rwb27/Instruments-MechanicalTester/cad/renders/0_main_view.png

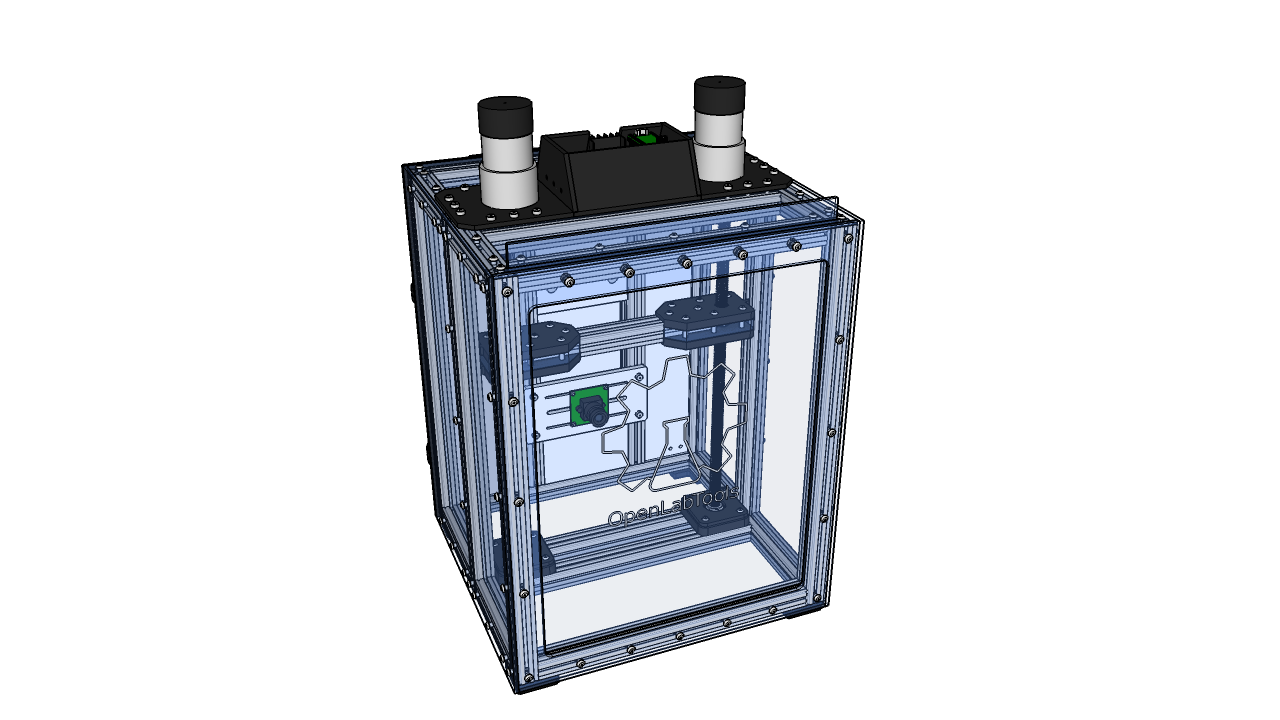
cad/renders/0_main_view.png
