rwb27/Instruments-MechanicalTester/cad/renders/2_top.png

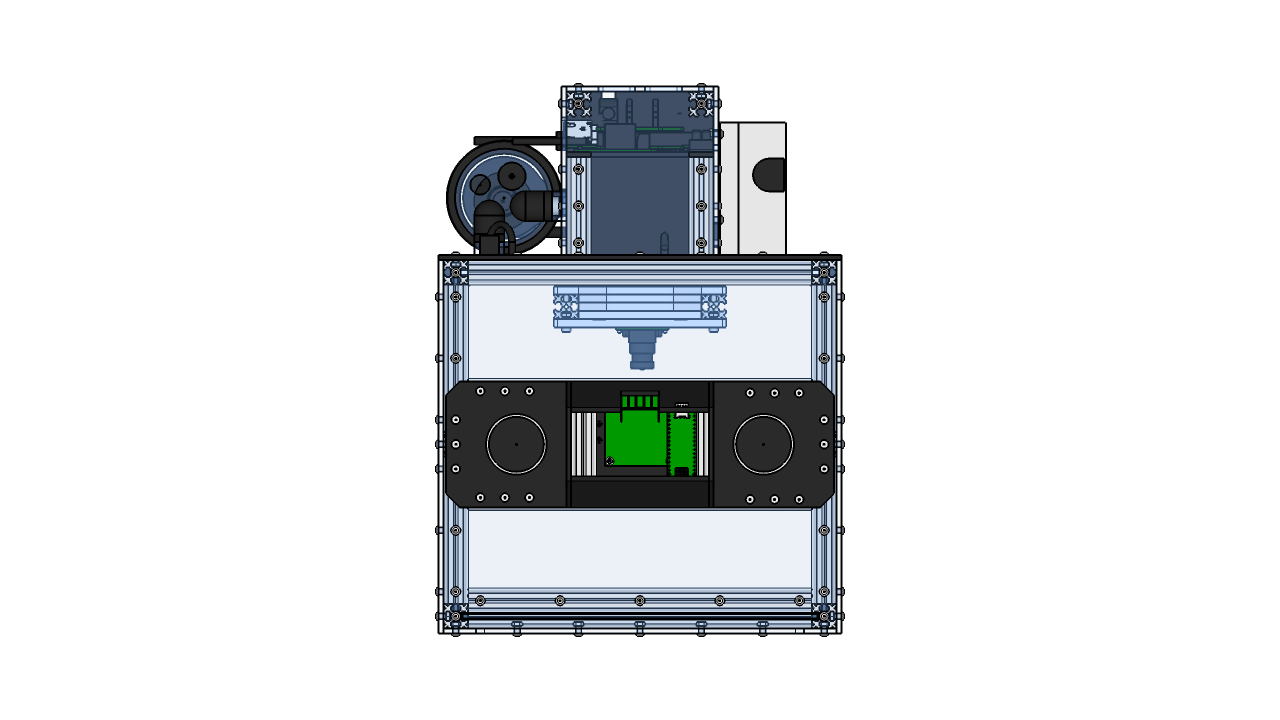
cad/renders/2_top.png
