rwb27/Instruments-MechanicalTester/cad/renders/2_top_small.png

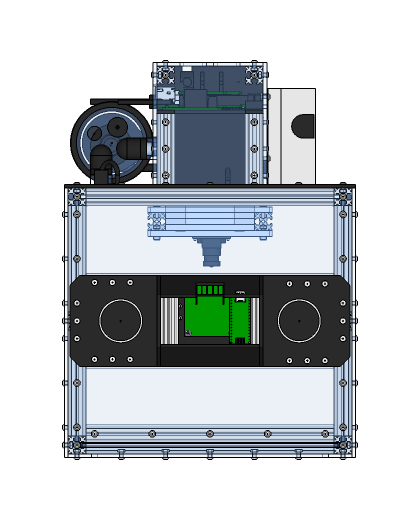
cad/renders/2_top_small.png
