rwb27/Instruments-MechanicalTester/cad/renders/3_front_small.png

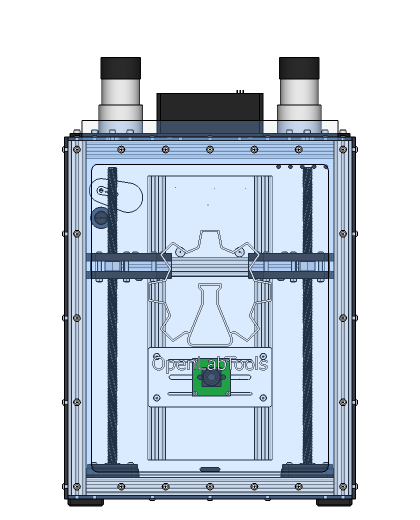
cad/renders/3_front_small.png
