rwb27/Instruments-MechanicalTester/cad/renders/4_right.png

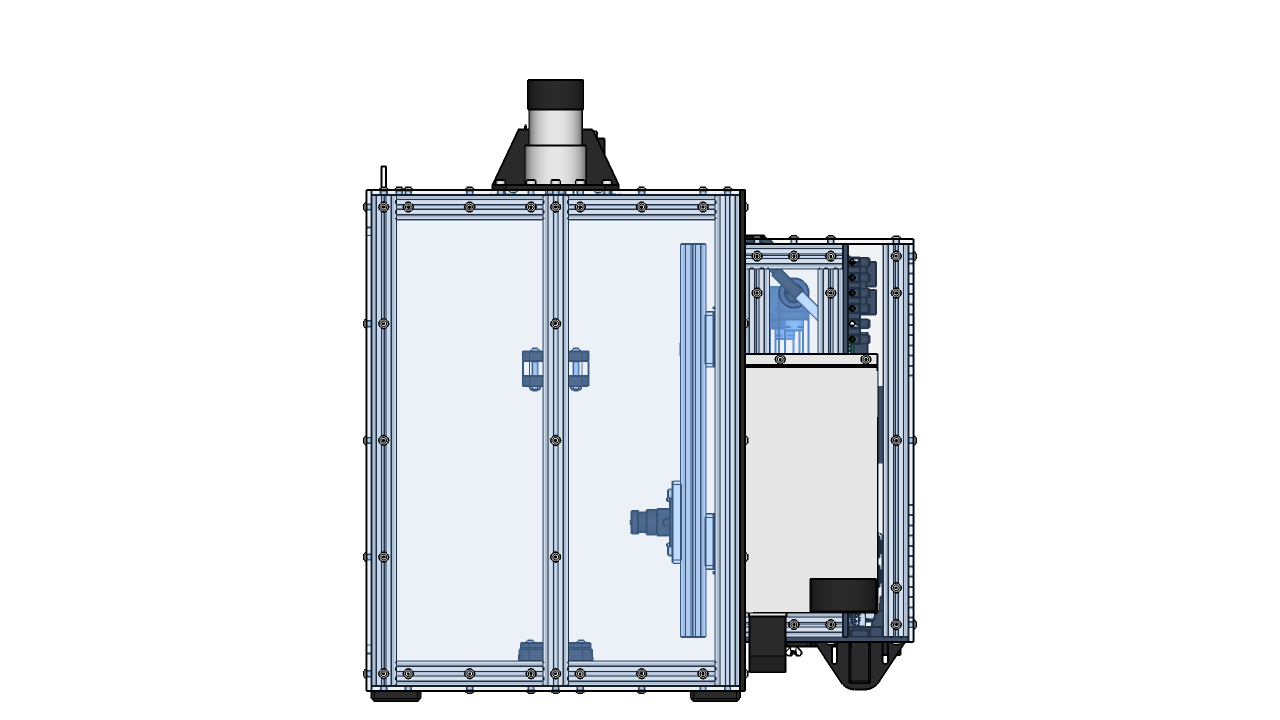
cad/renders/4_right.png
