rwb27/Instruments-MechanicalTester/cad/renders/4_right_small.png

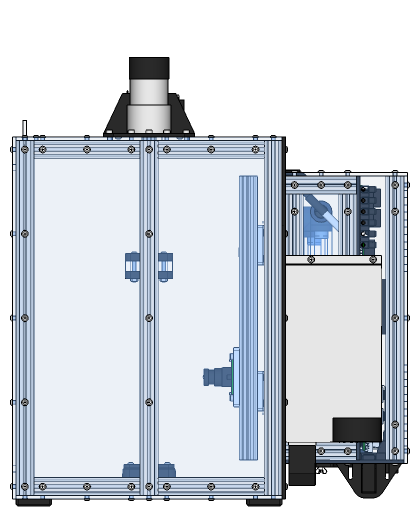
cad/renders/4_right_small.png
