rwb27/Instruments-MechanicalTester/cad/renders/5_back.png

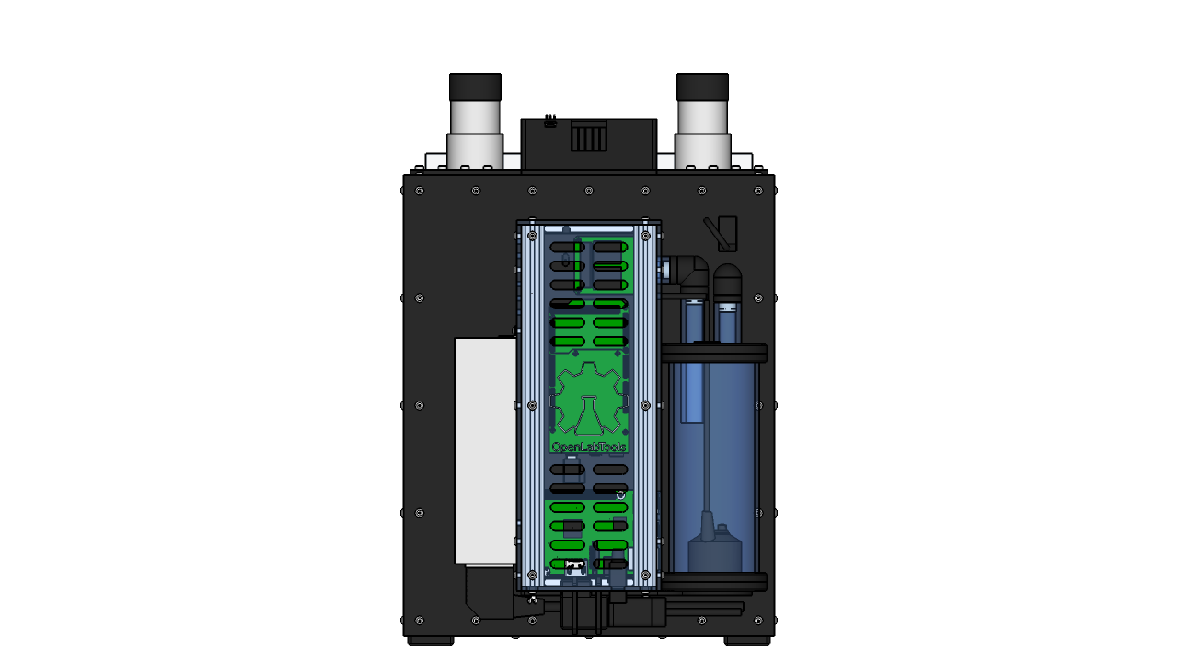
cad/renders/5_back.png
