rwb27/Instruments-MechanicalTester/cad/renders/5_back_small.png

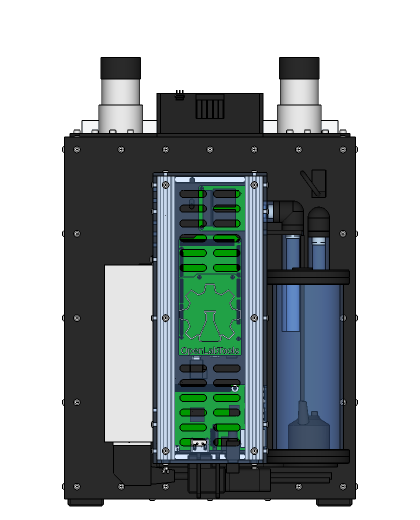
cad/renders/5_back_small.png
