rwb27/Instruments-MechanicalTester/cad/renders/8_cross_section.png

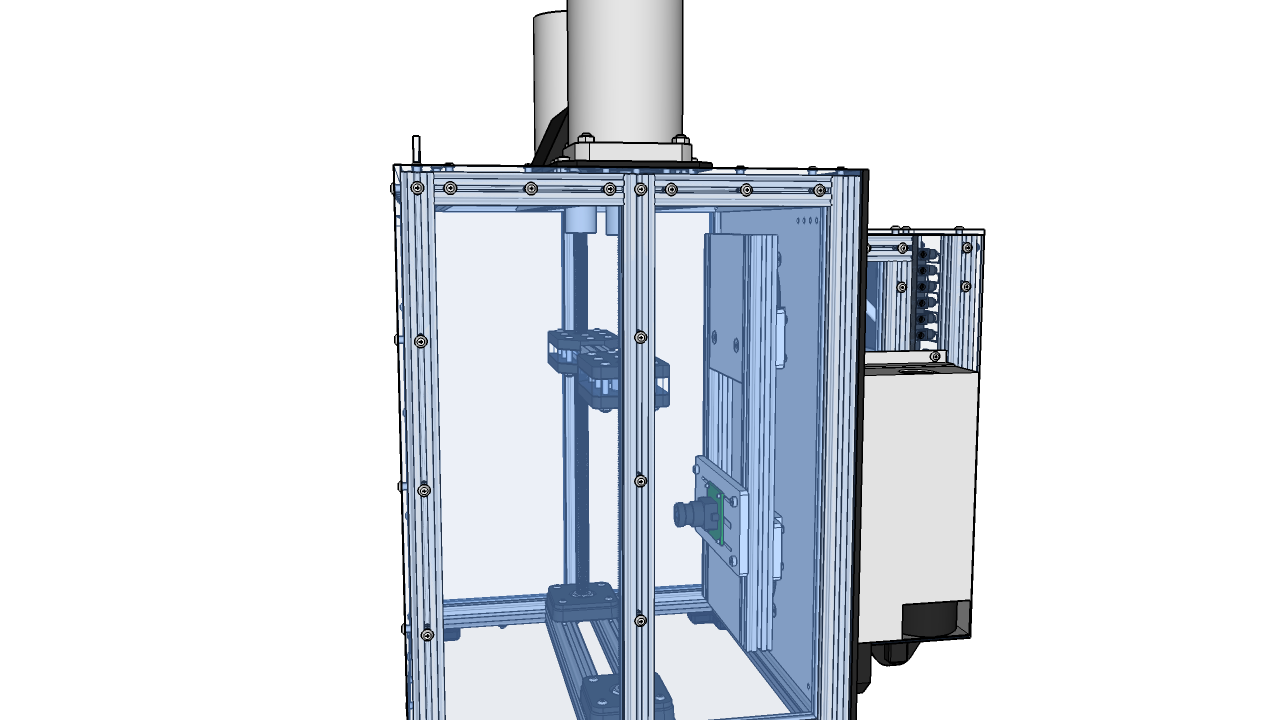
cad/renders/8_cross_section.png
