rwb27/Instruments-MechanicalTester/cad/renders/8_cross_section_small.png

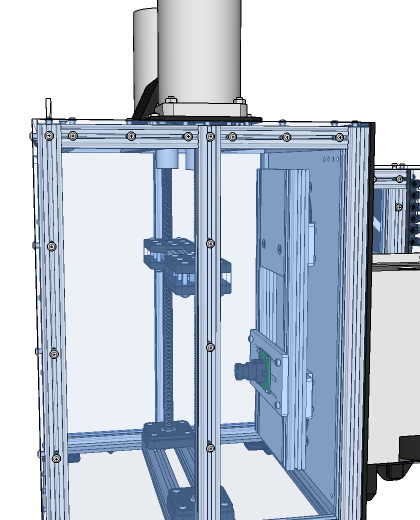
cad/renders/8_cross_section_small.png
