rwb27/Instruments-MechanicalTester/docs/images/instrument_views.jpg

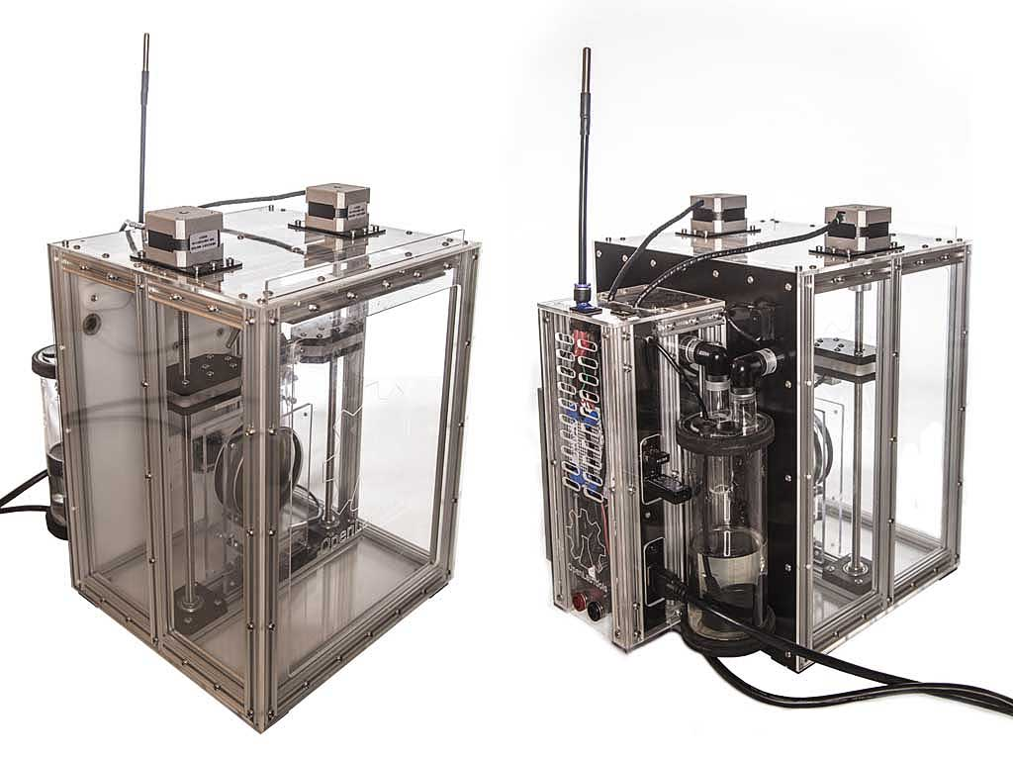
docs/images/instrument_views.jpg
