rwb27/Instruments-MechanicalTester/cad/panels/dxf_files/servo_flap.dxf

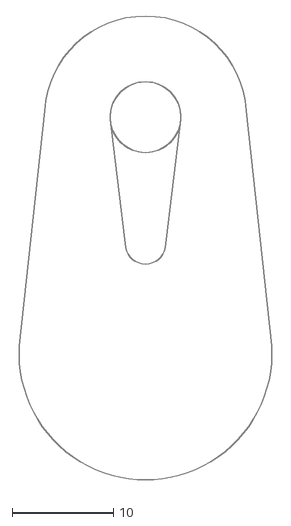
[picture p31: CAD file, 2016-01-02]
cad/panels/dxf_files/servo_flap.dxf
25.5 x 46.5
