rwb27/Instruments-MechanicalTester/cad/panels/dxf_files/humidity_rubber_bumper_bottom.dxf

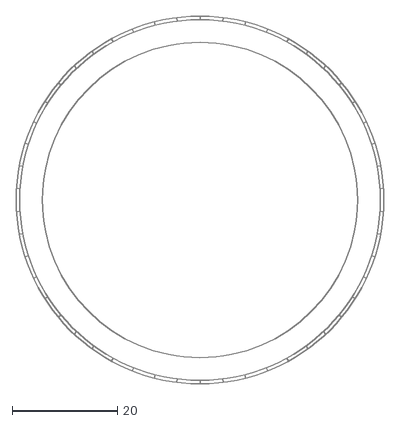
[picture p33: CAD file, 2016-01-02]
cad/panels/dxf_files/humidity_rubber_bumper_bottom.dxf
70.0 x 70.0
