rwb27/Instruments-MechanicalTester/cad/panels/dxf_files/humidity_end_cap.dxf

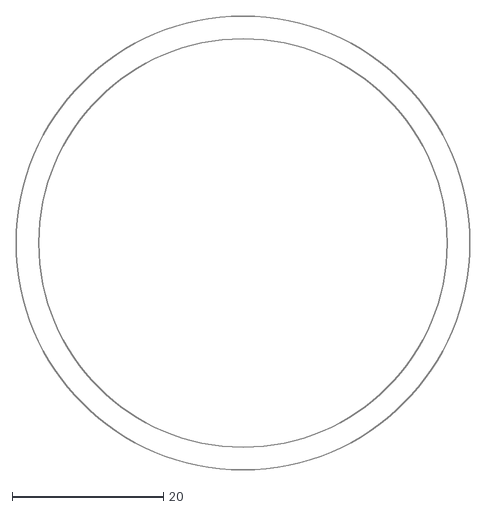
[picture p34: CAD file, 2016-01-02]
cad/panels/dxf_files/humidity_end_cap.dxf
60.0 x 60.0
