rwb27/Instruments-MechanicalTester/cad/panels/dxf_files/fan_mounting.dxf

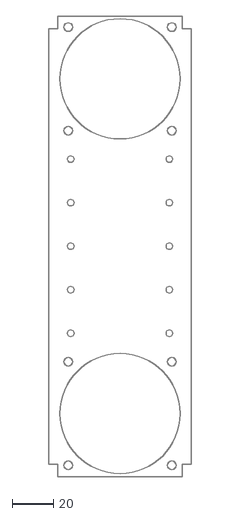
[picture p35: CAD file, 2016-01-02]
cad/panels/dxf_files/fan_mounting.dxf
69.0 x 222.0
