rwb27/Instruments-MechanicalTester/cad/panels/dxf_files/rear_module_back_double_glazing.dxf

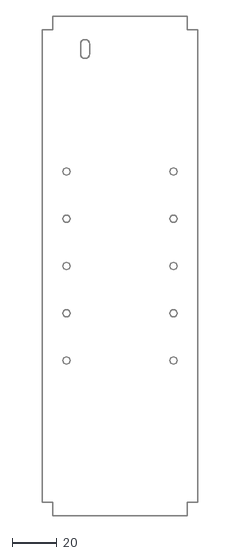
[picture p36: CAD file, 2016-01-02]
cad/panels/dxf_files/rear_module_back_double_glazing.dxf
69.0 x 222.0
