rwb27/Instruments-MechanicalTester/cad/panels/dxf_files/heater_reflector_plate.dxf

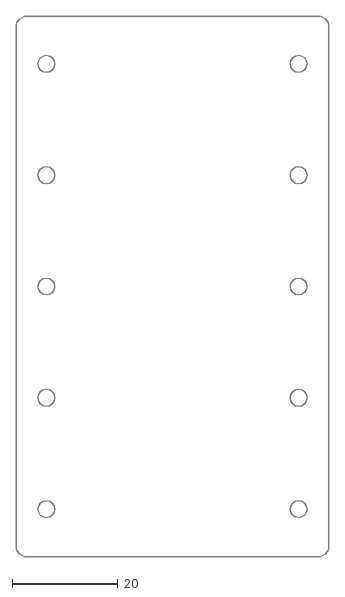
[picture p37: CAD file, 2016-01-02]
cad/panels/dxf_files/heater_reflector_plate.dxf
59.0 x 102.0
