rwb27/Instruments-MechanicalTester/cad/panels/dxf_files/rear_module_humidity_side.dxf

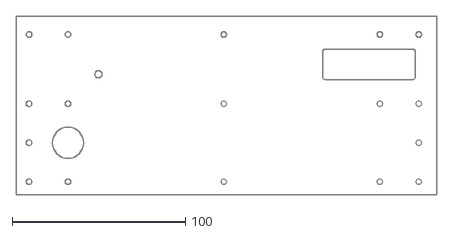
[picture p38: CAD file, 2016-01-01]
cad/panels/dxf_files/rear_module_humidity_side.dxf
243.0 x 103.0
