rwb27/Instruments-MechanicalTester/cad/panels/dxf_files/rear_module_bottom_face.dxf

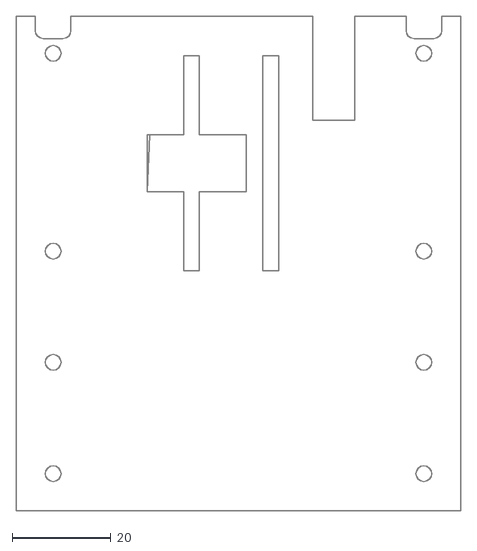
[picture p39: CAD file, 2016-01-01]
cad/panels/dxf_files/rear_module_bottom_face.dxf
90.0 x 100.0
