rwb27/Instruments-MechanicalTester/cad/panels/dxf_files/rear_module_electronics.dxf

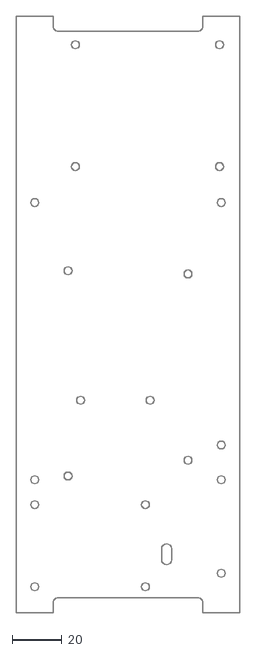
[picture p40: CAD file, 2016-01-01]
cad/panels/dxf_files/rear_module_electronics.dxf
90.0 x 240.0
