rwb27/Instruments-MechanicalTester/cad/panels/dxf_files/hdmi_support_2.dxf

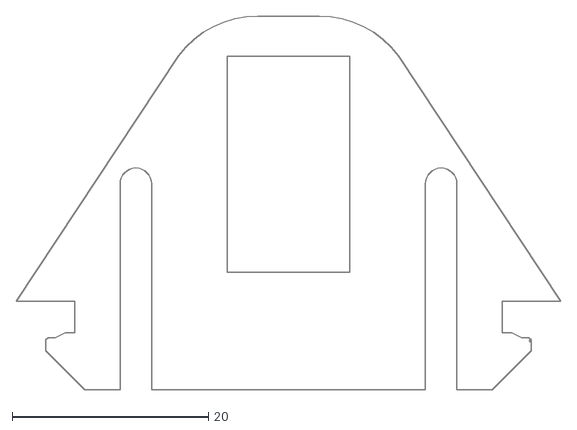
[picture p41: CAD file, 2015-12-31]
cad/panels/dxf_files/hdmi_support_2.dxf
55.5 x 38.1
