rwb27/Instruments-MechanicalTester/cad/panels/dxf_files/rear_module_back_face.dxf

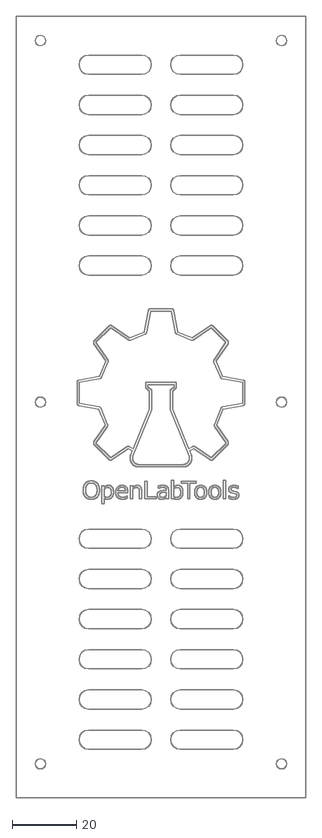
[picture p43: CAD file, 2015-12-28]
cad/panels/dxf_files/rear_module_back_face.dxf
90.0 x 243.0
