rwb27/Instruments-MechanicalTester/cad/panels/dxf_files/nema_17_mount.dxf

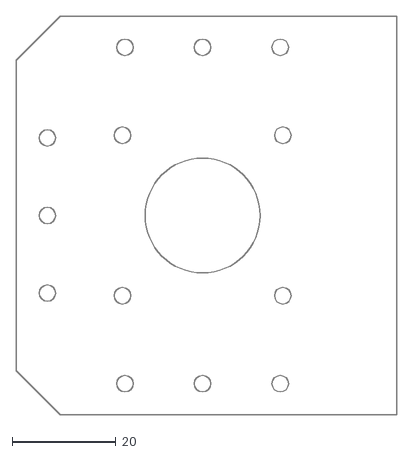
[picture p45: CAD file, 2015-12-27]
cad/panels/dxf_files/nema_17_mount.dxf
73.5 x 77.0
