rwb27/Instruments-MechanicalTester/cad/panels/dxf_files/gantry_spacer.dxf

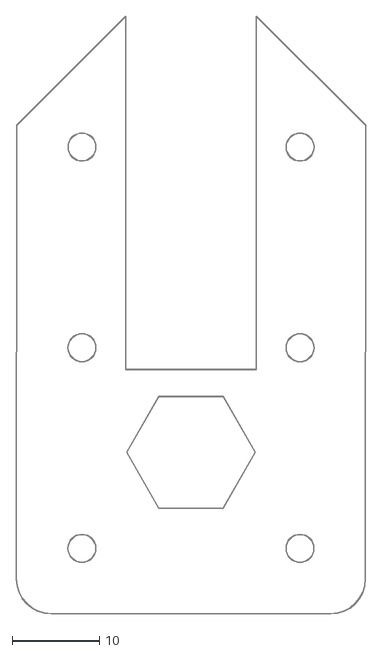
[picture p46: CAD file, 2015-12-23]
cad/panels/dxf_files/gantry_spacer.dxf
40.0 x 68.5
