rwb27/Instruments-MechanicalTester/cad/panels/dxf_files/front_frame.dxf

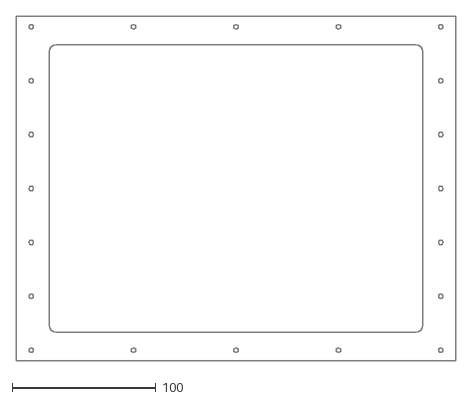
[picture p47: CAD file, 2015-12-23]
cad/panels/dxf_files/front_frame.dxf
306.0 x 240.0
