rwb27/Instruments-MechanicalTester/cad/panels/dxf_files/delrin_plate.dxf

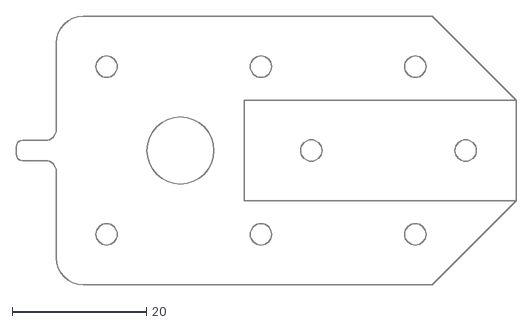
[picture p48: CAD file, 2015-12-23]
cad/panels/dxf_files/delrin_plate.dxf
74.5 x 40.0
