rwb27/Instruments-MechanicalTester/cad/panels/dxf_files/humidity_chamber_top_face.dxf

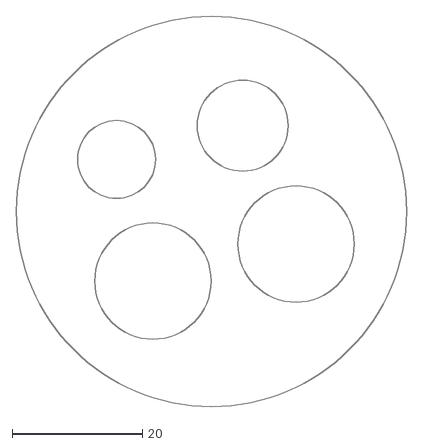
[picture p49: CAD file, 2015-12-23]
cad/panels/dxf_files/humidity_chamber_top_face.dxf
60.0 x 60.0
