rwb27/Instruments-MechanicalTester/cad/panels/dxf_files/baffle_spacer.dxf

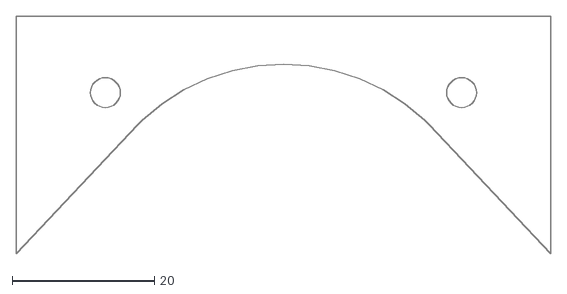
[picture p50: CAD file, 2015-12-23]
cad/panels/dxf_files/baffle_spacer.dxf
75.0 x 33.4
