rwb27/Instruments-MechanicalTester/cad/panels/dxf_files/side.dxf

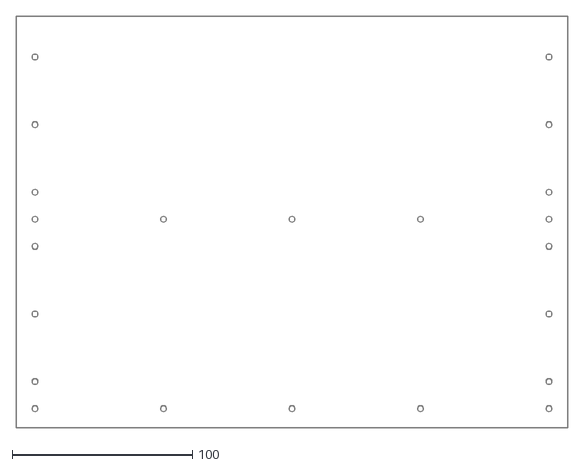
[picture p51: CAD file, 2015-12-23]
cad/panels/dxf_files/side.dxf
306.0 x 228.0
