rwb27/Instruments-MechanicalTester/cad/panels/dxf_files/front_door.dxf

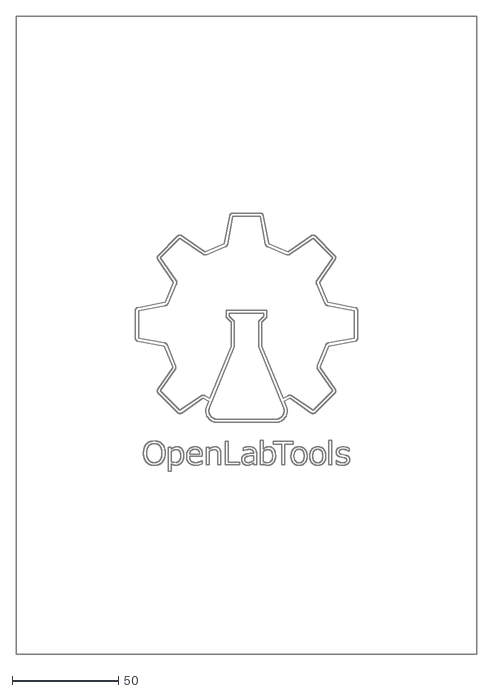
[picture p52: CAD file, 2015-12-23]
cad/panels/dxf_files/front_door.dxf
216.5 x 300.0
