rwb27/Instruments-MechanicalTester/cad/panels/dxf_files/rear_module_top_face.dxf

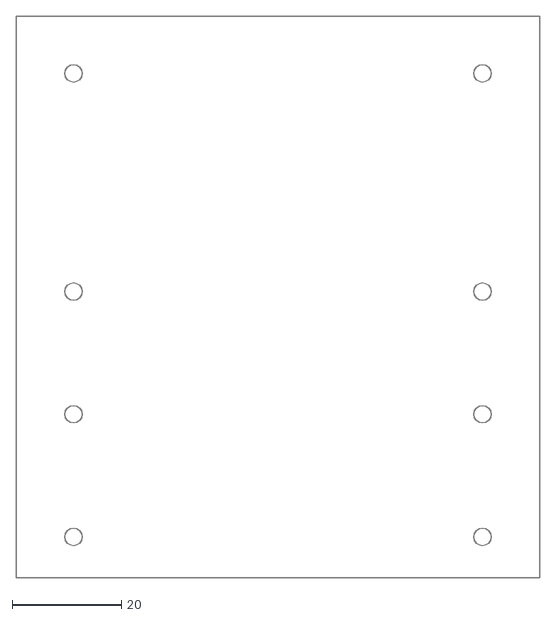
[picture p53: CAD file, 2015-12-23]
cad/panels/dxf_files/rear_module_top_face.dxf
96.0 x 103.0
