rwb27/Instruments-MechanicalTester/cad/panels/dxf_files/baffle_mount.dxf

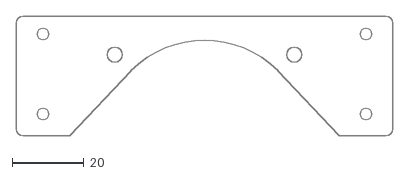
[picture p54: CAD file, 2015-12-23]
cad/panels/dxf_files/baffle_mount.dxf
105.0 x 33.4
