rwb27/Instruments-MechanicalTester/cad/panels/dxf_files/baffle_front_plate.dxf

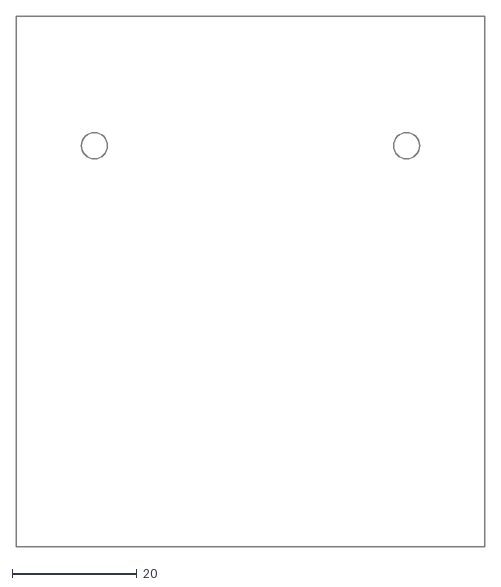
[picture p55: CAD file, 2015-12-23]
cad/panels/dxf_files/baffle_front_plate.dxf
75.0 x 85.0
