rwb27/Instruments-MechanicalTester/cad/panels/dxf_files/bottom_face.dxf

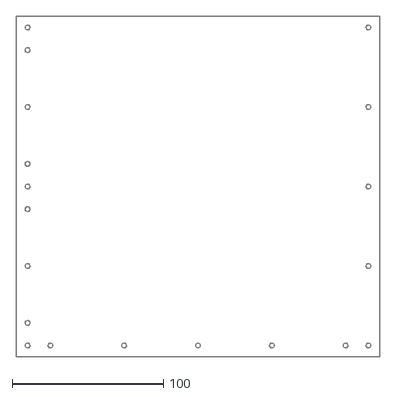
[picture p56: CAD file, 2015-12-23]
cad/panels/dxf_files/bottom_face.dxf
240.0 x 225.0
