rwb27/Instruments-MechanicalTester/cad/panels/dxf_files/back_face.dxf

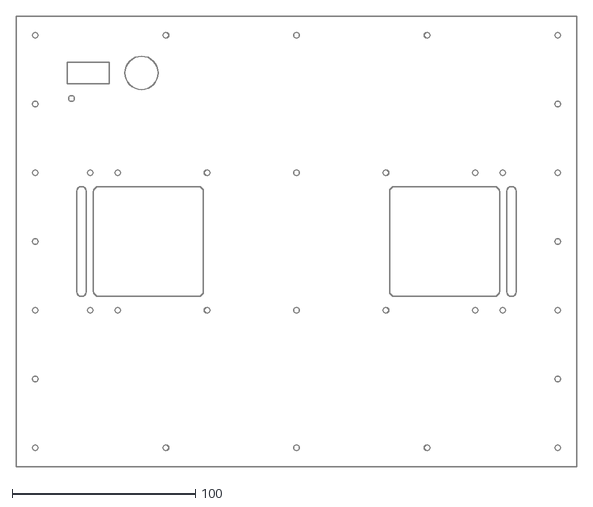
[picture p57: CAD file, 2015-12-23]
cad/panels/dxf_files/back_face.dxf
306.0 x 246.0
