rwb27/Instruments-MechanicalTester/cad/panels/dxf_files/bearing_top.dxf

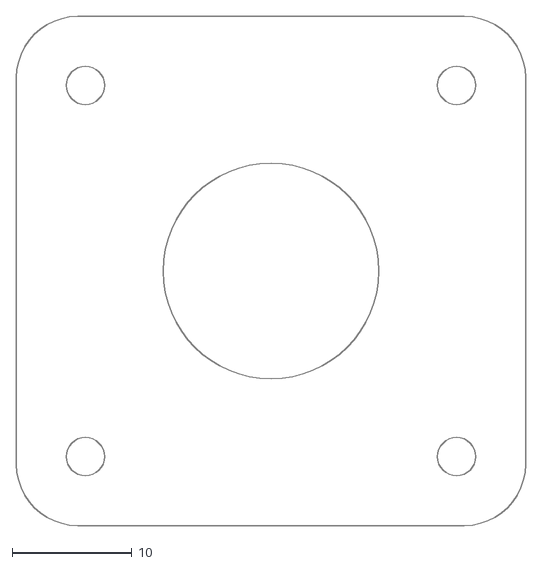
[picture p58: CAD file, 2015-12-23]
cad/panels/dxf_files/bearing_top.dxf
42.5 x 42.5
