rwb27/Instruments-MechanicalTester/cad/panels/dxf_files/rear_module_humidity_side_double_glazing.dxf

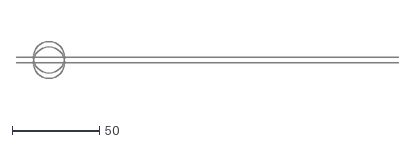
[picture p59: CAD file, 2015-12-23]
cad/panels/dxf_files/rear_module_humidity_side_double_glazing.dxf
219.0 x 21.0
