rwb27/Instruments-MechanicalTester/cad/panels/dxf_files/camera_mounting_plate.dxf

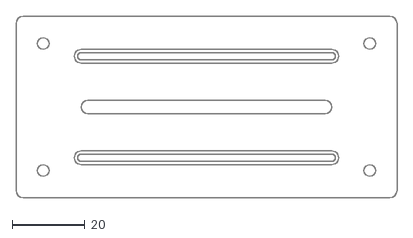
[picture p60: CAD file, 2015-12-23]
cad/panels/dxf_files/camera_mounting_plate.dxf
105.0 x 50.0
