rwb27/Instruments-MechanicalTester/cad/panels/dxf_files/humidity_support.dxf

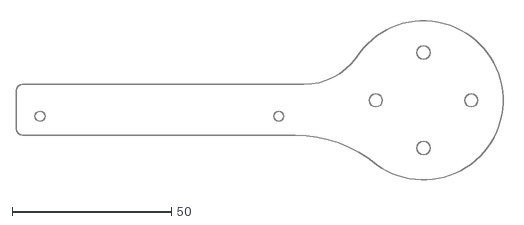
[picture p61: CAD file, 2015-12-23]
cad/panels/dxf_files/humidity_support.dxf
154.5 x 53.1
