rwb27/Instruments-MechanicalTester/cad/panels/dxf_files/inner_back_wall.dxf

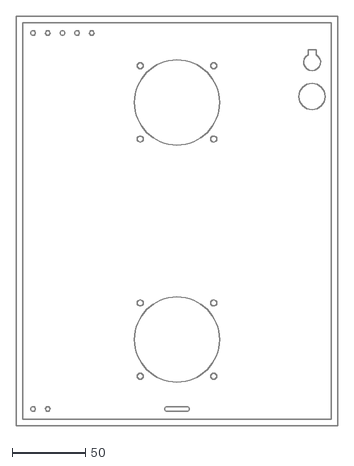
[picture p62: CAD file, 2015-12-23]
cad/panels/dxf_files/inner_back_wall.dxf
219.0 x 279.0
