rwb27/Instruments-MechanicalTester/cad/panels/dxf_files/top_double_glazing_front.dxf

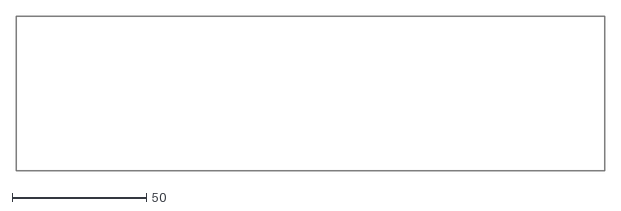
[picture p63: CAD file, 2015-12-14]
cad/panels/dxf_files/top_double_glazing_front.dxf
219.0 x 57.4
