rwb27/Instruments-MechanicalTester/cad/panels/dxf_files/rear_module_psu_side_double_glazing.dxf

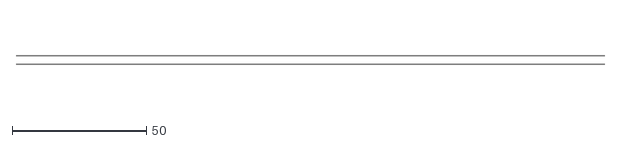
[picture p64: CAD file, 2015-12-14]
cad/panels/dxf_files/rear_module_psu_side_double_glazing.dxf
219.0 x 3.00
