rwb27/Instruments-MechanicalTester/cad/panels/dxf_files/top_double_glazing_back.dxf

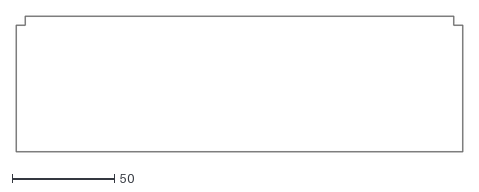
[picture p65: CAD file, 2015-12-14]
cad/panels/dxf_files/top_double_glazing_back.dxf
219.0 x 66.5
