rwb27/Instruments-MechanicalTester/cad/panels/dxf_files/side_double_glazing.dxf

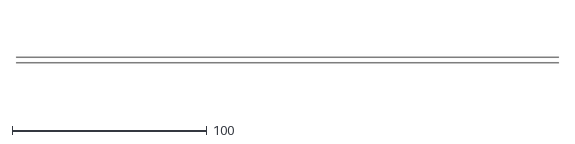
[picture p66: CAD file, 2015-12-14]
cad/panels/dxf_files/side_double_glazing.dxf
279.0 x 3.00
