rwb27/Instruments-MechanicalTester/cad/panels/dxf_files/bottom_double_glazing.dxf

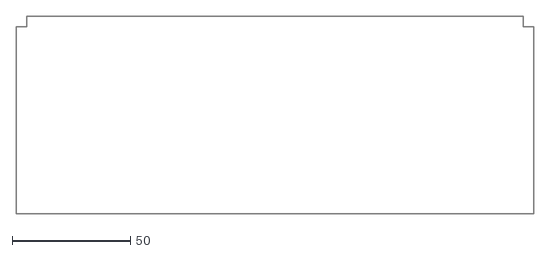
[picture p67: CAD file, 2015-12-14]
cad/panels/dxf_files/bottom_double_glazing.dxf
219.0 x 83.5
