rwb27/Instruments-MechanicalTester/cad/panels/dxf_files/bottom_double_glazing_middle.dxf

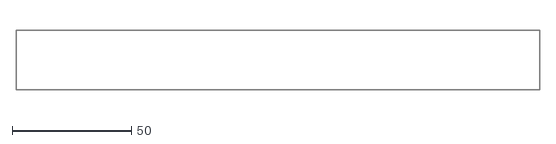
[picture p68: CAD file, 2015-12-14]
cad/panels/dxf_files/bottom_double_glazing_middle.dxf
219.0 x 25.0
