rwb27/Instruments-MechanicalTester/cad/subassemblies/side_wall/renders/0_start_with_side_panel.png

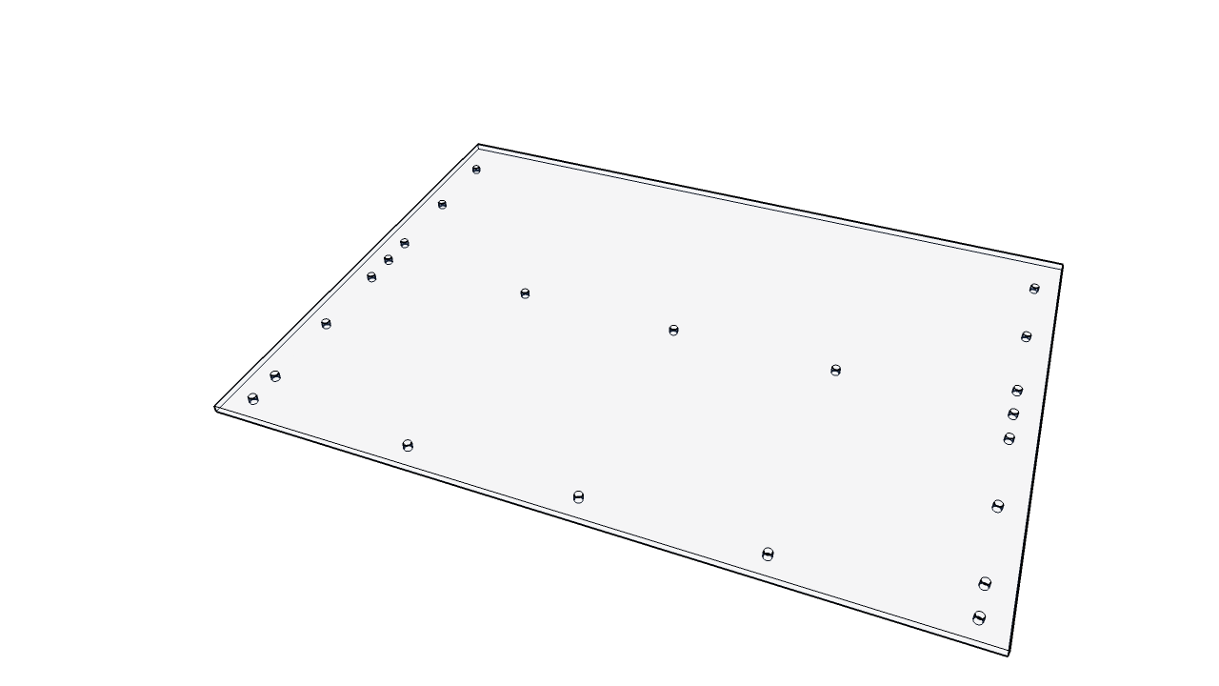
cad/subassemblies/side_wall/renders/0_start_with_side_panel.png
