rwb27/Instruments-MechanicalTester/cad/subassemblies/side_wall/renders/4_add_double_glazing.png

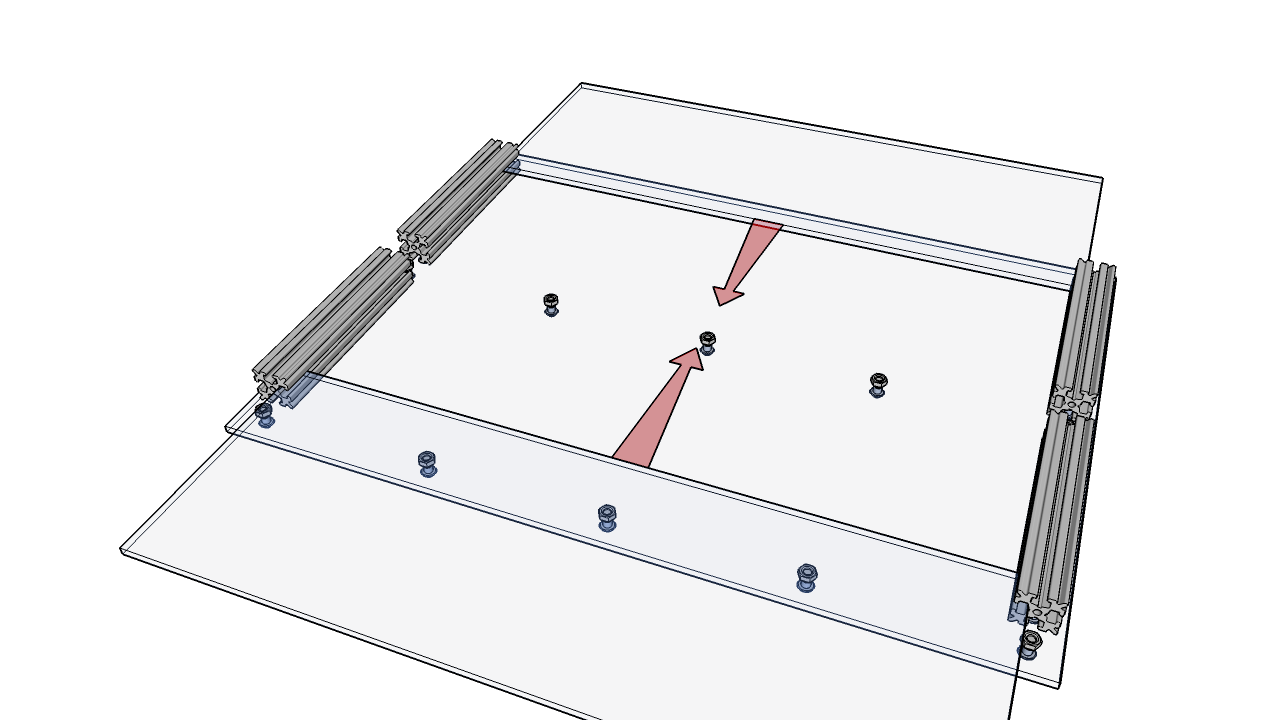
cad/subassemblies/side_wall/renders/4_add_double_glazing.png
