rwb27/Instruments-MechanicalTester/cad/subassemblies/side_wall/renders/6_add_verticals.png

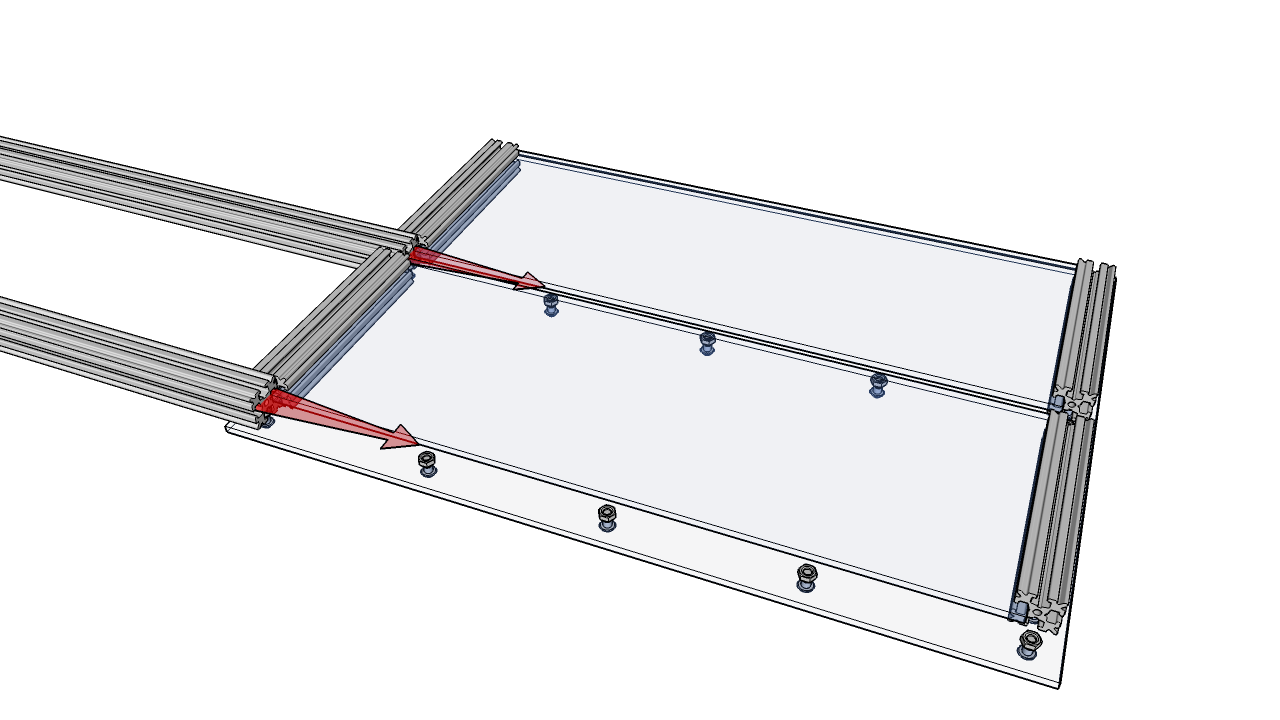
cad/subassemblies/side_wall/renders/6_add_verticals.png
